BennyHoang/Sensor-combo/M2M-assignment/pir.h

#ifndef PIR_SENSOR_H
#define PIR_SENSOR_H PIR_SENSOR_H

#include "application.h"

#define PIR_PIN D0
#define LED_PIN D7

class PIRSensor{
public:
  PIRSensor();
  void init();
  bool calibrated();
  void readSensorValue();
  void outputMotion();
  bool getMotionStatus();
  void setMotionStatus(bool motion);
private:
  int _calibrationTime;
  int _val;
  int _state;
  bool _motion;
};

#endif
